dinther/tapbox/case/texture.png

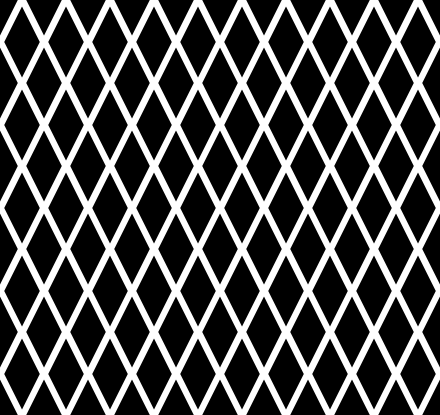
case/texture.png
