dinther/tapbox/docs/AI Case Render.png

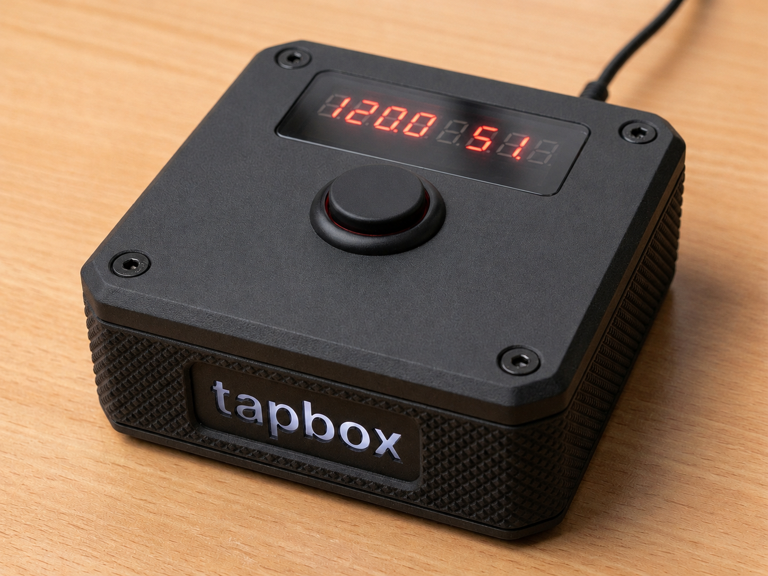
docs/AI Case Render.png
