dinther/tapbox/docs/beatline eye transparent.png

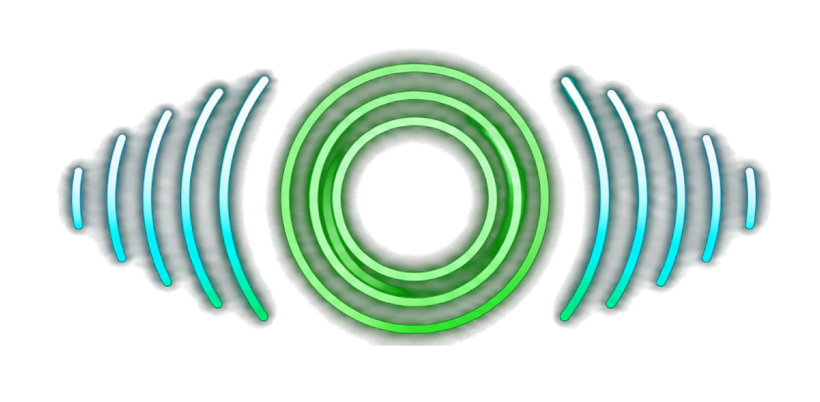
docs/beatline eye transparent.png
