dinther/tapbox/docs/beatline transparent.png

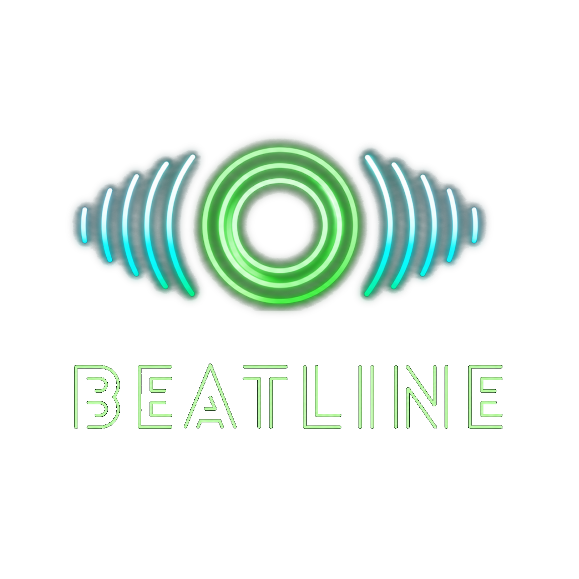
docs/beatline transparent.png
