dinther/tapbox/docs/beatline_text_transparent.png

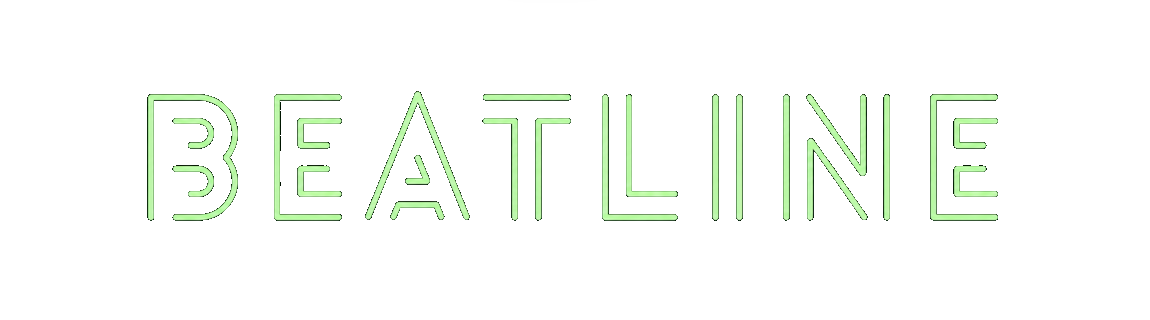
docs/beatline_text_transparent.png
