dinther/tapbox/docs/Case.png

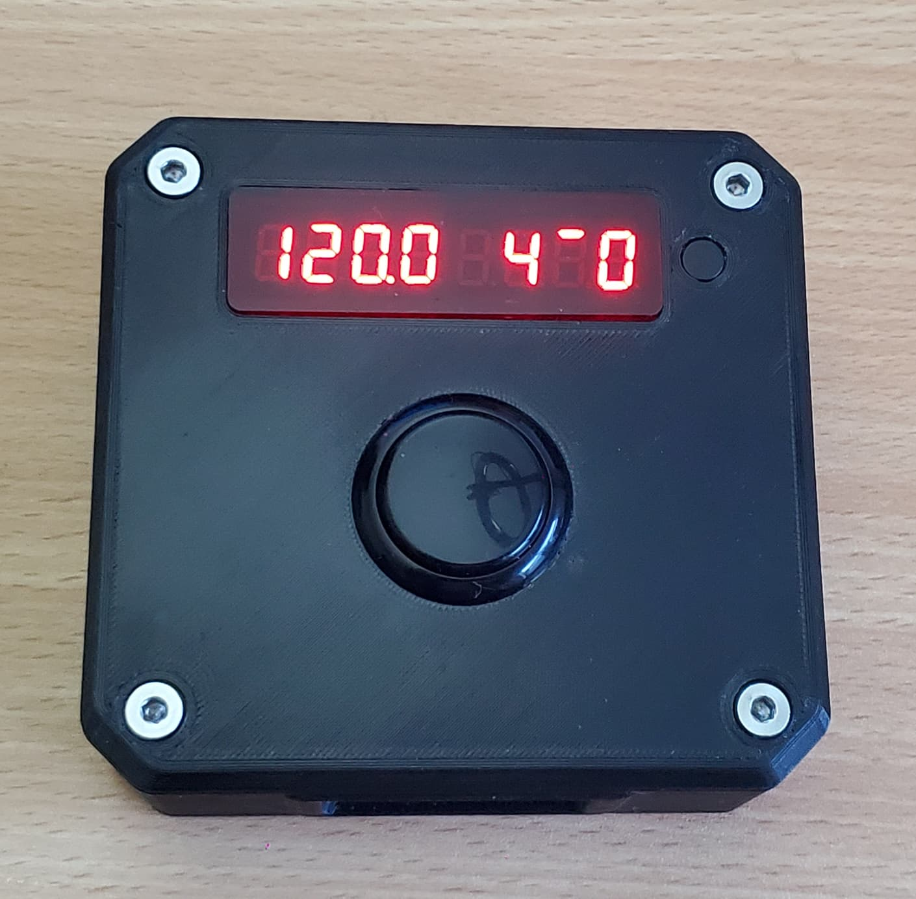
docs/Case.png
