dinther/tapbox/component_images/3.5mm_stereo_sensing_socket.png

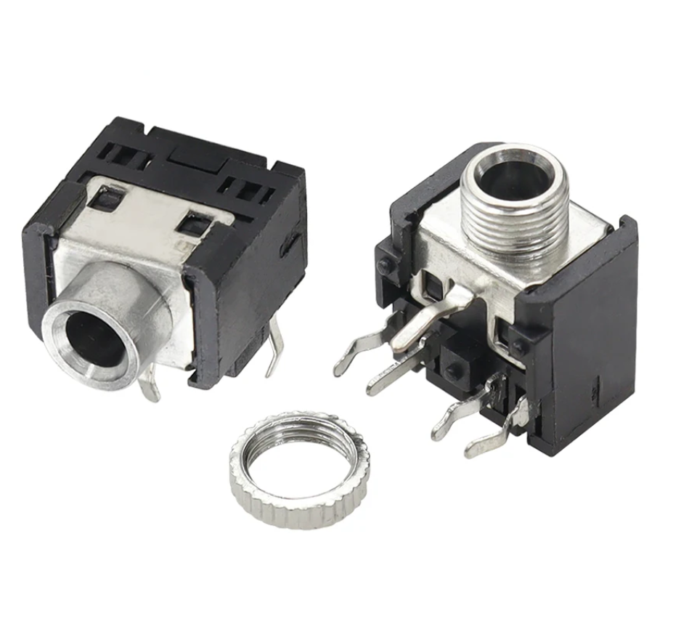
component_images/3.5mm_stereo_sensing_socket.png
