dinther/tapbox/component_images/26650_battery.png

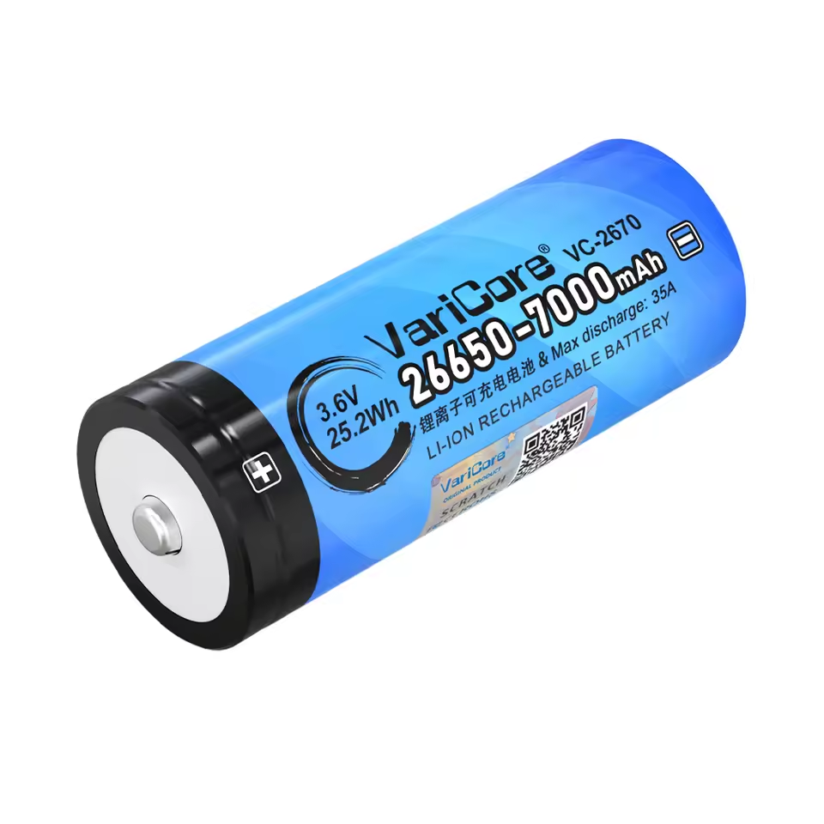
component_images/26650_battery.png
