dinther/tapbox/component_images/INMP441.png

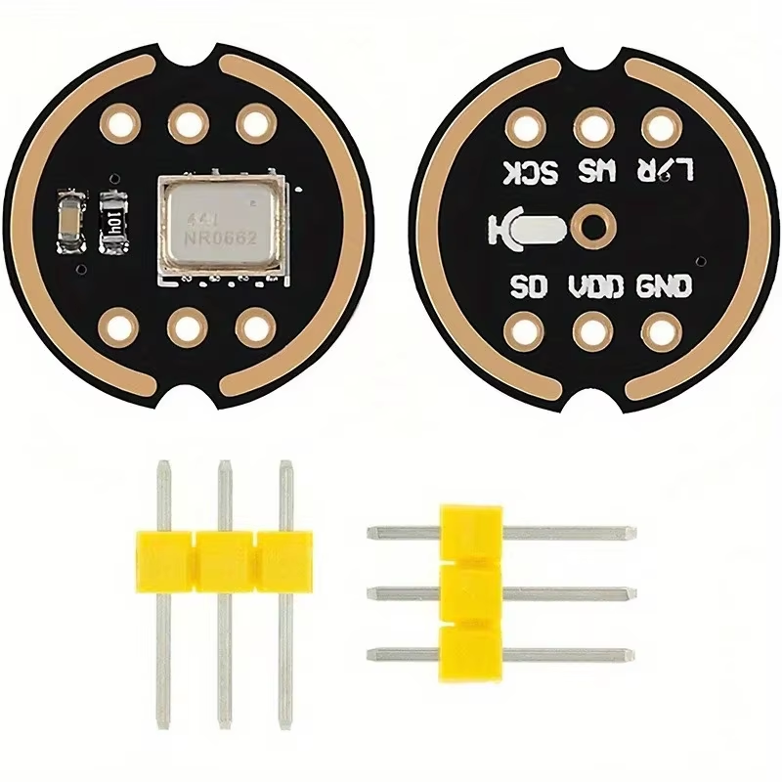
component_images/INMP441.png
