dinther/tapbox/component_images/PCM1808.png

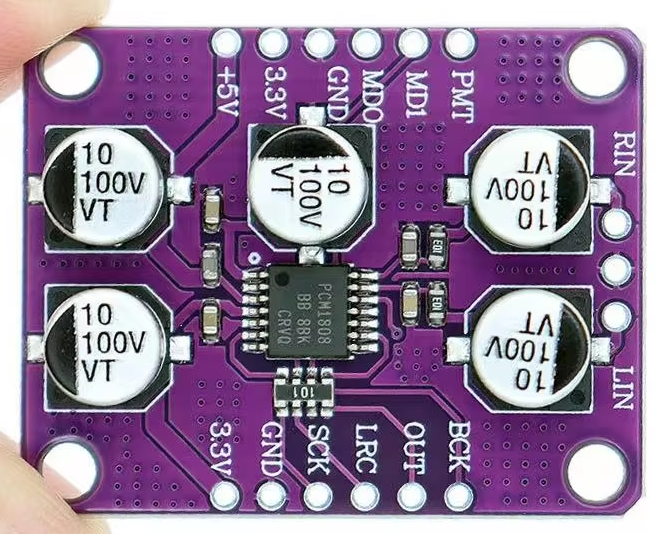
component_images/PCM1808.png
