dinther/tapbox/component_images/Rock_switch.png

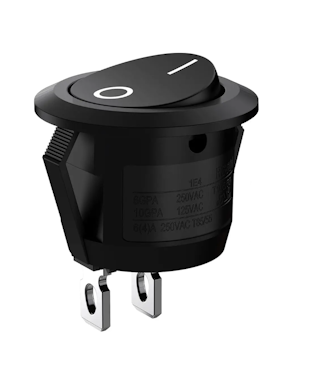
component_images/Rock_switch.png
