dinther/tapbox/component_images/TP4056_charger_board.png

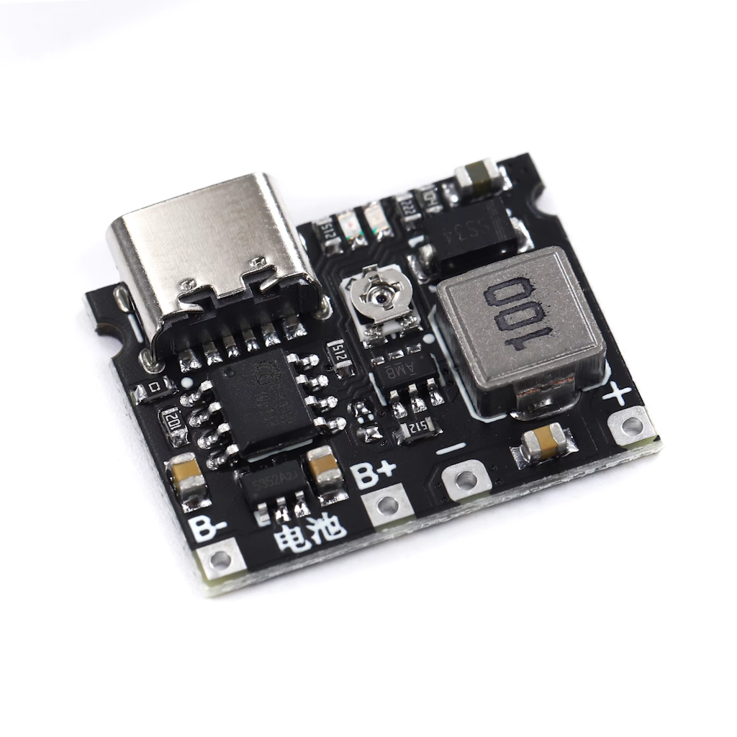
component_images/TP4056_charger_board.png
