dinther/tapbox/component_images/WT32-eth01_board.jpeg

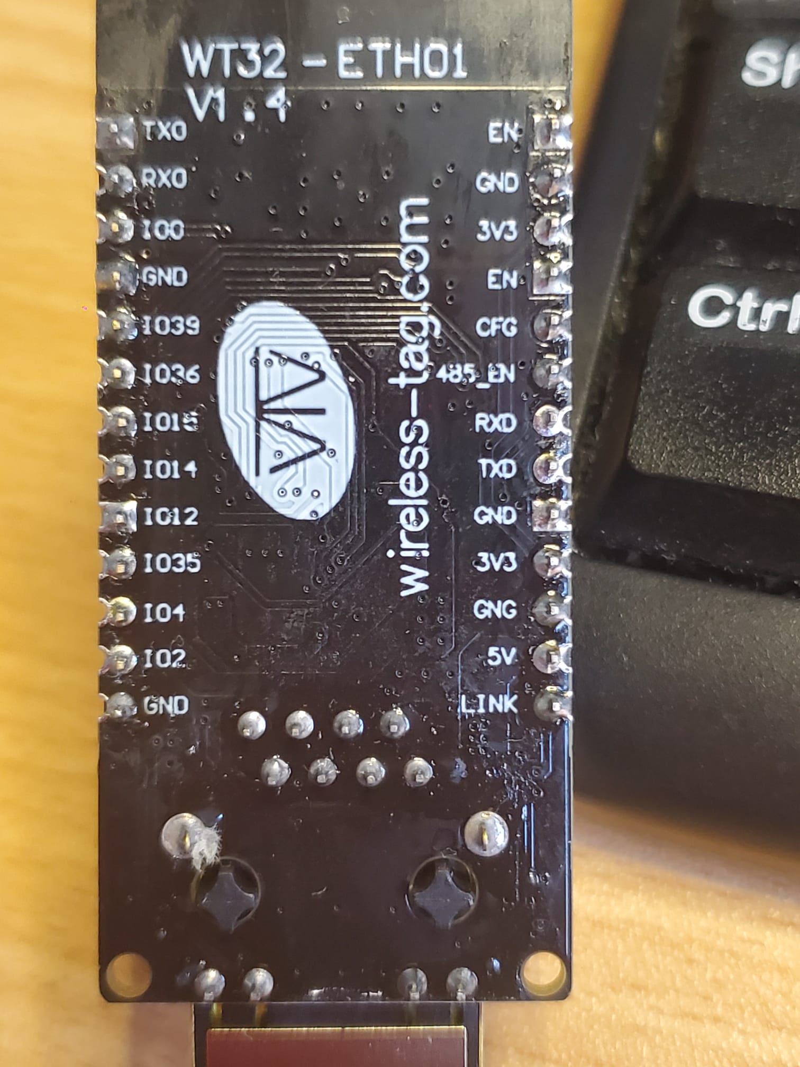
component_images/WT32-eth01_board.jpeg
